taubrafi/IoTsightV3/Case/Picatinny Rail.STL

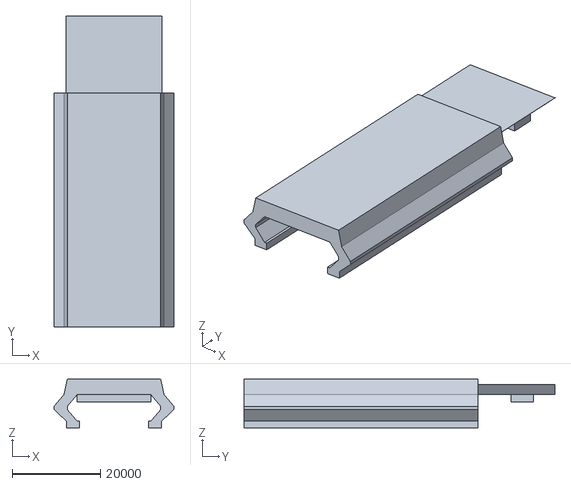
[picture p30: CAD file, 2016-12-10]
Case/Picatinny Rail.STL
27158.2 x 70401.0 x 11074.4
