taubrafi/IoTsightV3/Case/Body3.STL

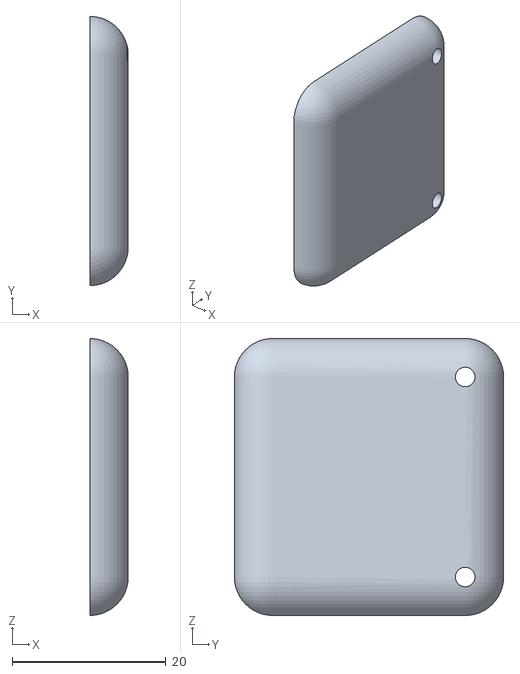
[picture p31: CAD file, 2016-12-10]
Case/Body3.STL
5.00 x 35.0 x 36.0
